jc-SpaceXp/Spekky-Matrix/freertos_gdb.py

"""
These commands must only be used after pxCurrentTCB is initialized.
Task-specific breakpoint may have undefined behaviour in multiprocess environments.
"""

import enum
import gdb


class FreeRTOSList():
    """Python class representation of FreeRTOS' List_t struct in C.

    Parameters
    ----------
    uxNumberOfItems : gdb.Value (UBaseType_t)
    pxIndex : gdb.Value (ListItem_t *)
    xListEnd : gdb.Value (MiniListItem_t)
    head : gdb.Value (xLIST_ITEM *)
        Pointer to first item in the list.
    cast_type : gdb.Type
        Type of the objects owning items in the list.
    """

    def __init__(self, freertos_list, cast_type_str):
        """
        Parameters
        ----------
        freertos_list : gdb.Value (List_t)
            An inferior variable of type List_t whose data to use.
        cast_type_str : str
            The type of objects that own each ListItem_t in the list.
        """

        self.uxNumberOfItems = freertos_list['uxNumberOfItems']
        self.pxIndex = freertos_list['pxIndex']
        self.xListEnd = freertos_list['xListEnd']

        self.head = self.xListEnd['pxNext']
        self.cast_type = gdb.lookup_type(cast_type_str).pointer()

    def __iter__(self):
        curr_node = self.head
        while self.uxNumberOfItems > 0 and curr_node != self.xListEnd.address:
            tmp_node = curr_node.dereference()
            data = tmp_node['pvOwner'].cast(self.cast_type)
            yield data
            curr_node = tmp_node['pxNext']

class TaskList(enum.Enum):
    """All FreeRTOS task lists to scan for tasks from.
    
    Parameters
    ----------
    symbol : str
        The variable name of the task list.
    state: str
        'B' - Blocked
        'R' - Ready
        'D' - Deleted (waiting clean up)
        'S' - Suspended, or Blocked without a timeout
    """

    READY = ('pxReadyTasksLists', 'R')
    #SUSPENDED = ('xSuspendedTaskList', 'S')
    DELAYED_1 = ('xDelayedTaskList1', 'B')
    DELAYED_2 = ('xDelayedTaskList2', 'B')
    #WAIT_TERM = ('xTasksWaitingTermination', 'D')

    def __init__(self, symbol, state):
        self.symbol = symbol
        self.state = state

class TaskVariable(enum.Enum):
    """Variables of TCB_t to display. Refer to FreeRTOS' task.c file for
       more documentation.

    Parameters
    ----------
    symbol : str
        The name of the variable in TCB_t.
    get_var_fn: Callable
        A function to get the variable as a gdb.Value, then cast it to the
        appropriate Python type.
    config_check: str, optional
        The config define to check if the variable is enabled.
    """

    PRIORITY = ('uxPriority', 'get_int_var', '')
    STACK = ('pxStack', 'get_hex_var', '')
    NAME = ('pcTaskName', 'get_string_var', '')
    STACK_END = ('pxEndOfStack', 'get_hex_var', 'configRECORD_STACK_HIGH_ADDRESS')
    CRITICAL_NESTING = ('uxCriticalNesting', 'get_int_var', 'portCRITICAL_NESTING_IN_TCB')
    TCB_NUM = ('uxTCBNumber', 'get_int_var', 'configUSE_TRACE_FACILITY')
    MUTEXES = ('uxMutexesHeld', 'get_int_var', 'configUSE_MUTEXES')
    RUN_TIME = ('ulRunTimeCounter', 'get_int_var', 'configGENERATE_RUN_TIME_STATS')

    def __init__(self, symbol, get_var_fn_str, config_check):
        self.symbol = symbol
        self.get_var_fn = getattr(self, get_var_fn_str)
        self.config_check = config_check

    def is_configured(self):
        """Checks if the defines enabling this variable are set."""
        return (self.config_check == '' 
                or gdb.parse_and_eval(self.config_check))

    def get_int_var(self, tcb):
        return int(tcb[self.symbol])

    def get_hex_var(self, tcb):
        return hex(int(tcb[self.symbol]))

    def get_string_var(self, tcb):
        return tcb[self.symbol].string()

def get_current_tcbs():
    """Returns a list of the currently running tasks. The elements are
       gdb.Values with inferior type (TCB_t *)."""

    current_tcbs_arr = []
    
    current_tcbs = gdb.parse_and_eval('pxCurrentTCB')

    if current_tcbs.type.code == gdb.TYPE_CODE_ARRAY:
        cpus = current_tcbs.type.range()
        for cpu in range(cpus[0], cpus[1] + 1):
            current_tcbs_arr.append(current_tcbs[cpu])
    else:
        current_tcbs_arr.append(current_tcbs)
    
    return current_tcbs_arr

def tasklist_to_rows(tasklist, state, current_tcbs):
    """Parses a task list into rows that can be displayed.
    
    Parameters
    ----------
    tasklist : gdb.Value (List_t)
    state : str
    current_tcbs : list of gdb.Value (TCB_t *)

    Returns
    -------
    rows : list of lists
        Each element is a list containing information to display for a task.
    """

    rows = []
    pythonic_list = FreeRTOSList(tasklist, 'TCB_t')

    for task_ptr in pythonic_list:
        if task_ptr == 0:
            print("Task pointer is NULL. Stack corruption?")
    
        row = []
        task_tcb = task_ptr.referenced_value()
    
        row.append(str(task_ptr))
        row.append(state)
        if task_ptr in current_tcbs:
            row.append(current_tcbs.index(task_ptr))
        else:
            row.append('')
        for tcb_var in TaskVariable:
            if tcb_var.is_configured():
                row.append(tcb_var.get_var_fn(task_tcb))
        
        rows.append(row)

    return rows

def get_header():
    """Returns table headers describing each piece of task info."""

    headers = ["ID", "STATE", "CPU"]

    for taskvar in TaskVariable:
        if taskvar.is_configured():
            headers.append(taskvar.name)

    return headers

# New
def print_table(table, headers=None):
    if headers:
        table.insert(0, headers)

    max_column = [0] * len(table[0])
    for _, row in enumerate(table):
        for k, _ in enumerate(max_column):
            max_column[k] = max(len(str(row[k])), max_column[k])

    # print formatted
    for i, row in enumerate(table):
        # print row
        for k, _ in enumerate(max_column):
            print(str(row[k]).rjust(max_column[k]), end=' ')
        print(end='\n')
        # print header separator
        if headers and i == 0:
            header_separator = ' '.join([''.rjust(max_column[i], '-') for i in range(len(max_column))])
            print(header_separator)


class FreeRTOSBreakpoint (gdb.Breakpoint):
    def __init__(self, task_name, spec):
        self.task_name = task_name
        super(FreeRTOSBreakpoint, self).__init__(spec)

    def stop (self):
        current_task_names = [tcb['pcTaskName'].string() for tcb in get_current_tcbs()]
        return self.task_name in current_task_names

class FreeRTOS(gdb.Command):
    def __init__(self):
        super(FreeRTOS, self).__init__('freertos', gdb.COMMAND_USER, gdb.COMPLETE_COMMAND, True)

class FreeRTOSTaskInfo(gdb.Command):
    """Displays FreeRTOS tasks and information."""
  
    def __init__ (self):
        super (FreeRTOSTaskInfo, self).__init__ ("freertos tasks", gdb.COMMAND_USER)

    def invoke (self, arg, from_tty):
        table = []
        current_tcbs = get_current_tcbs()

        for tasklist in TaskList:
            tasklist_val = gdb.parse_and_eval(tasklist.symbol)

            if tasklist_val.type.code == gdb.TYPE_CODE_ARRAY:
                #only used for pxReadyTaskLists, because it has a list for every priority.
                priorities = tasklist_val.type.range()
                for priority in range(priorities[0], priorities[1] + 1):
                    table.extend(tasklist_to_rows(tasklist_val[priority], tasklist.state, current_tcbs))
            else:
                table.extend(tasklist_to_rows(tasklist_val, tasklist.state, current_tcbs))

        if len(table) == 0:
            print ("There are currently no tasks. The program may not have "
                   "created any tasks yet.")
            return

        #print(print_table(table, headers=get_header()))
        print_table(table, headers=get_header())

class FreeRTOSCreateBreakpoint(gdb.Command):
    """Create a breakpoint that will only get tripped by the specific task."""

    def __init__(self):
        super (FreeRTOSCreateBreakpoint, self).__init__ ("freertos break", gdb.COMMAND_USER, gdb.COMPLETE_SYMBOL)

    def invoke (self, arg, from_tty):
        argv = gdb.string_to_argv(arg)

        if len(argv) == 0:
            print ("No arguments given. Must have 2 arguments in "
                   "order of \"target_task target_location\".")
            return

        target_task = argv[0]
        target_function = argv[1]

        FreeRTOSBreakpoint(target_task, target_function)

FreeRTOS()
FreeRTOSTaskInfo()
FreeRTOSCreateBreakpoint()
