jc-SpaceXp/Spekky-Matrix/tests/fft_processing_main.c

#include "greatest.h"
#include "fft_processing_suite.h"


GREATEST_MAIN_DEFS();

int main(int argc, char **argv)
{
	(void) argc;
	(void) argv;

	GREATEST_MAIN_BEGIN();

	RUN_SUITE(fft_suite);

	GREATEST_MAIN_END(); // exapnds to a return statement
}
