jc-SpaceXp/Spekky-Matrix/tests/fermion_mic_check.py

# Output from DATA_OUT of 1KHz sine wave PulseView data
l_channel_list = [
    0x00000000
    , 0x00000000
    , 0x00000000
    , 0x00000000
    , 0x00000000
    , 0x00000000
    , 0x00000000
    , 0xfffe7e00
    , 0x00003a00
    , 0x0003efc0
    , 0x0003d7c0
    , 0x00047c00
    , 0x0001abf0
    , 0x000569e0
    , 0xfffe9400
    , 0x0009f5c0
    , 0xfff84200
    , 0x001333f0
    , 0xffeb4a00
    , 0x0026de00
    , 0xffcbc5f0
    , 0x006899f0
    , 0xfec629f0
    , 0x0033b600
    , 0x0456c3f0
    , 0x0385e400
    , 0x0397b7f8
    , 0x0329bdf0
    , 0x033afbf0
    , 0x030d6df0
    , 0x03161200
    , 0x03043800
    , 0x0308ae00
    , 0x03025bf0
    , 0x03051ff2
    , 0x0306a9f0
    , 0x03076800
    , 0x03066ff0
    , 0x03089200
    , 0x030873d0
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
]
