jc-SpaceXp/Spekky-Matrix/inc/sine_1hz_dma_test.h

#ifndef SINE_1HZ_LUT_H
#define SINE_1HZ_LUT_H

#include <stdint.h>

const int16_t sine_1hz_dma_lut_test[1024] = {
	0
	, 972
	, 601
	, -601
	, -972
	, 0
	, 972
	, 601
	, -601
	, -972
	, 0
	, 972
	, 601
	, -601
	, -972
	, 0
	, 972
	, 601
	, -601
	, -972
	, 0
	, 972
	, 601
	, -601
	, -972
	, 0
	, 972
	, 601
	, -601
	, -972
	, 0
	, 972
	, 601
	, -601
	, -972
	, 0
	, 972
	, 601
	, -601
	, -972
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
};

#endif /* SINE_1HZ_LUT_H */
