jc-SpaceXp/Spekky-Matrix/tests/py_fft.py

import numpy as np
import matplotlib.pyplot as plt
import matplotlib.ticker as mtick
import matplotlib.animation as animation
from functools import partial
from statistics import mean
from fermion_mic_check import l_channel_list

def dump_lists_to_file(fft_input, fft_output):
    expected_input = "py_sine_input_test.txt"
    outfile = open(expected_input, 'w')
    outfile.writelines('\n'.join(str(i).ljust(23) for i in fft_input))
    outfile.close()
    expected_output = "py_sine_output_fft_test.txt"
    outfile = open(expected_output, 'w')
    outfile.writelines('\n'.join(f'{c.real:0.09f}'.ljust(18) + f' {c.imag:+0.09f}j'
                                for c in fft_output))
    return None

def periodically_sampled_waveform(integer, freq, sampling_freq, total_samples, show_samples
                                 , show_plot, remove_dc, window):
    freq = freq
    fsamp = sampling_freq
    tsamp = 1.0/fsamp
    w = 2*np.pi*freq
    N = total_samples  # making N say 256 only works when tweaking fsamp and f so that most of the wave is captured
    tlen = N/fsamp
    t = np.arange(0, tlen, tsamp) # 1sec worth of samples == fsamples total
    tend = N/fsamp

    dc_only = False

    # Round to a value which stm32 can replicate
    int32_max = np.power(2, 31) - 1
    x = np.float32(np.sin(w*t))
    if integer:
        x = [int32_max] * int(N / 2)
        x[len(x):] = [0] * int(N / 2)
        if dc_only:
            x = [int32_max] * int(N)

    if remove_dc:
        x = x - mean(x)

    if window:
        x = x * np.blackman(N)

    if show_samples:
        print(x)

    if show_plot:
        plt.plot(t, x)
        plt.xlabel('Time, seconds (s)')
        plt.ylabel('Amplitude')
        plt.show()
    return x

def fft_conversion(sampled_waveform, show_conversion):
    X = np.complex64(np.fft.fft(sampled_waveform))

    if show_conversion:
        print(X)

    return X

def plot_fft_ifft_results(fft_results, sampling_freq, total_samples, animate):
    tsamp = 1.0/sampling_freq
    n = np.arange(total_samples)
    T = N/sampling_freq

    fig.suptitle('FFT and iFFT', y=0.995)

    fft_graph = np.abs(fft_results)
    fft_graph_label = 'FFT Amplitude'
    if decibel_fft:
        window_gain = 1
        acoustic_overload_point = 124
        dbfs_max = acoustic_overload_point
        fft_max = np.power(2, 31) - 1
        mag_ref_max = (fft_max * N) / 2
        if i2s_debug:
            amp_ref_max = np.power(2, 23) - 1
        # 0 values should represent -inf dB
        # if we set to a really low value we get a dB value below the noise floor
        # also C math.h log10 function expects argument to be > 0
        for i in range(len(fft_graph)):
            if fft_graph[i] == 0:
                fft_graph[i] = 0.8
        # Max value of FFT is 32-bits therefore mag_ref_max doesn't change
        # even though my I2S data is constrained to 24-bits
        fft_graph = (20 * np.log10(fft_graph / mag_ref_max))
        ax1.plot((n/T), fft_graph)
        ax1.set_ylim([-dbfs_max, 10])
        fft_graph_label = 'FFT Amplitude (dB FS)'

    ax1.grid()
    if not decibel_fft:
        ax1.stem((n/T), fft_graph)
    ax1.set_xlabel('Freq (Hz)')
    ax1.set_ylabel(fft_graph_label)
    if animate:
        if not decibel_fft:
            ax1.set_ylim([0.00, 2.50E11])
    if decibel_fft:
        secax1.plot(n, fft_graph)
    else:
        secax1.stem(n, fft_graph)
    secax1.tick_params(axis='x', which='major')
    secax1.set_xlabel('FFT Bins', labelpad=2.00)
    secax1.xaxis.set_label_position('top')

    ax2.plot(tsamp * n, np.fft.ifft(fft_results).real)
    ax2.set_xlabel('Time, seconds (s)')

    if not decibel_fft:
        ax1.yaxis.set_major_formatter(mtick.FormatStrFormatter('%.2e'))
    ax2.yaxis.set_major_formatter(mtick.ScalarFormatter(useMathText=True))

    return None

def gen_raw_data_iter():
    offset = 0
    fft_size = 64
    raw_data = l_channel_list
    while (offset + fft_size) < len(raw_data):
        yield offset
        offset += fft_size

def animate(frame, fft_fig, ifft_fig, fft_bins_fig, sampling_freq, fft_size):
    fft_fig.clear()
    fft_bins_fig.clear()
    ifft_fig.clear()
    x = l_channel_list[frame:fft_size+frame]
    fft_out = fft_conversion(x, show_conversion=False)
    plot_fft_ifft_results(fft_out, sampling_freq, fft_size, animate=True)
    #fig.savefig(f'{frame:04d}.png')
    return None

# Compare theoretical (i2s_debug == False) with actual (i2s_debug == True)
freq = 1000
fsamp = 1.0/60E-6 # fsamp is one period of WS (~i2s_samp / 2) (measured in PulseView)
N = 1024 # fft size (or sample count)
print_sampled_fft_input = False
plot_sampled_fft_input = False
print_fft_output = False
decibel_fft = True
plot_fft_output = True
integer = True
i2s_debug = True
remove_dc = True
window = True
dump_results_to_file = False
animate_fft = True

# Make global so animate and plot functions can both use
fig, (ax1, ax2) = plt.subplots(1, 2)
secax1 = ax1.twiny()

x = periodically_sampled_waveform(integer, freq, fsamp, N, print_sampled_fft_input
                                 , plot_sampled_fft_input, remove_dc, window)
if i2s_debug:
    offset = 0
    x = l_channel_list[offset:N+offset]

fft_out = fft_conversion(x, print_fft_output)
if plot_fft_output:
    if animate_fft:
        ani = animation.FuncAnimation(fig, partial(animate, fft_fig=ax1, ifft_fig=ax2
                                                  , fft_bins_fig=secax1
                                                  , sampling_freq=fsamp, fft_size=64)
                                     , frames=gen_raw_data_iter, interval=400, save_count=1
                                     , repeat_delay=3000)
    else:
        plot_fft_ifft_results(fft_out, fsamp, N, animate=False)
    plt.show()

if dump_results_to_file:
    dump_lists_to_file(x, fft_out)
